FelixJMaxwell/MechanicalKeyboard/Kicad Footprints/arduino_micro_shield.png

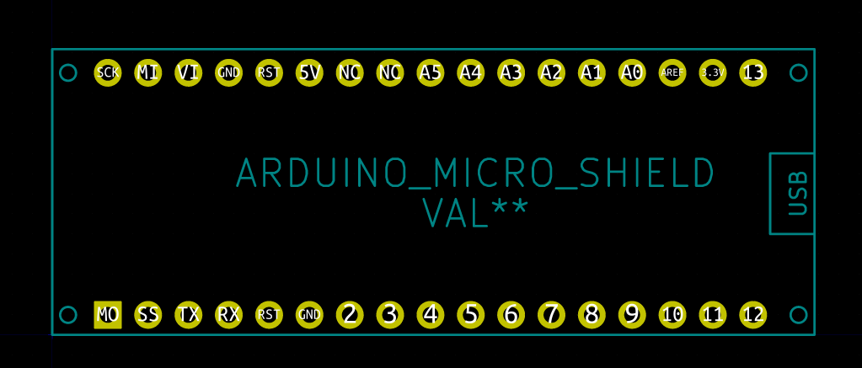
Kicad Footprints/arduino_micro_shield.png
