FelixJMaxwell/MechanicalKeyboard/Kicad Footprints/Stabilizer_Cherry_MX_7u.step

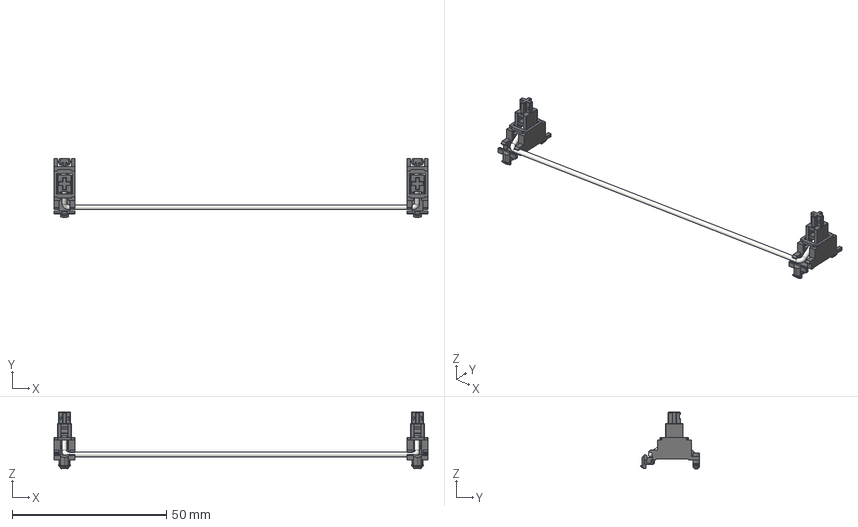
[picture p28: CAD file, 2021-05-09]
Kicad Footprints/Stabilizer_Cherry_MX_7u.step
121.1 x 19.2 x 18.3 mm
