FelixJMaxwell/MechanicalKeyboard/Kicad Footprints/Stabilizer_Cherry_MX_2u.step

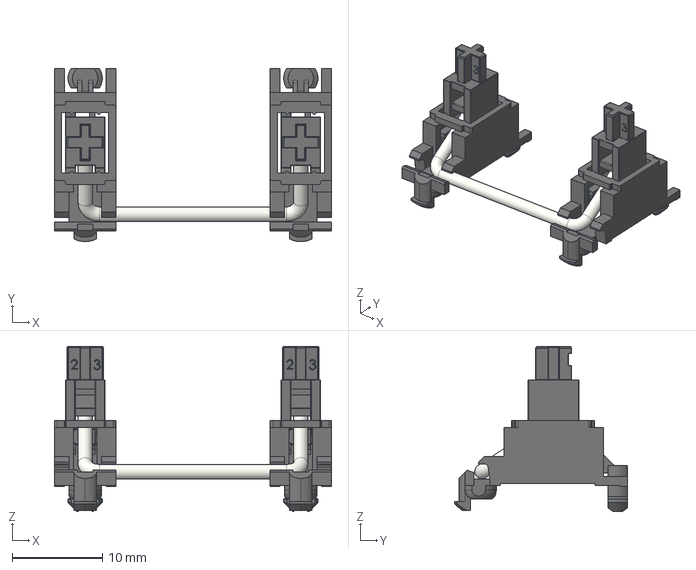
[picture p29: CAD file, 2021-05-09]
Kicad Footprints/Stabilizer_Cherry_MX_2u.step
30.7 x 19.2 x 18.3 mm
