FelixJMaxwell/MechanicalKeyboard/Kicad Footprints/Stabilizer_Cherry_MX_3u.step

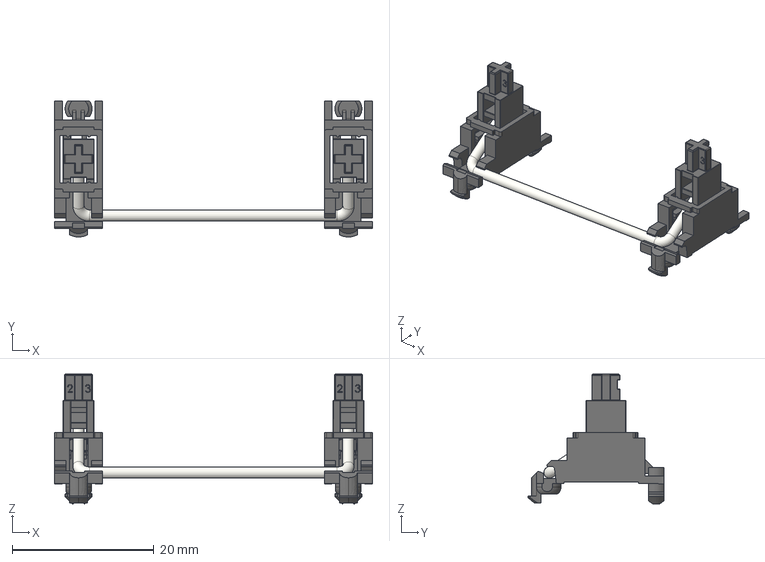
[picture p30: CAD file, 2021-05-09]
Kicad Footprints/Stabilizer_Cherry_MX_3u.step
44.9 x 19.2 x 18.3 mm
