FelixJMaxwell/MechanicalKeyboard/Kicad Footprints/SW_Cherry_MX_PCB.step

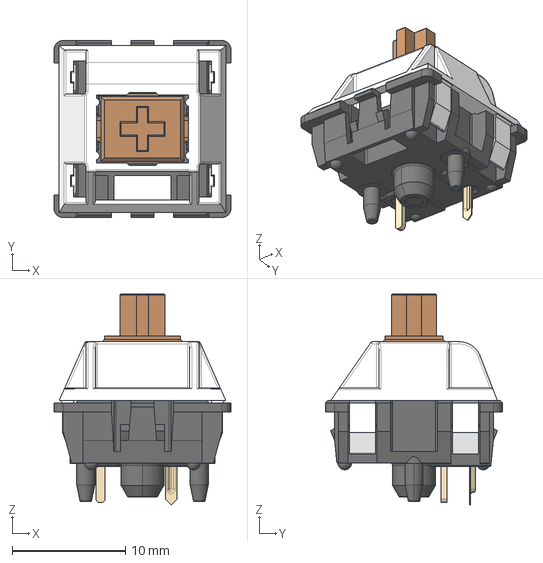
[picture p31: CAD file, 2021-05-09]
Kicad Footprints/SW_Cherry_MX_PCB.step
15.6 x 15.6 x 18.6 mm
