FelixJMaxwell/MechanicalKeyboard/Kicad Footprints/D_SOD-123 Soldered.step

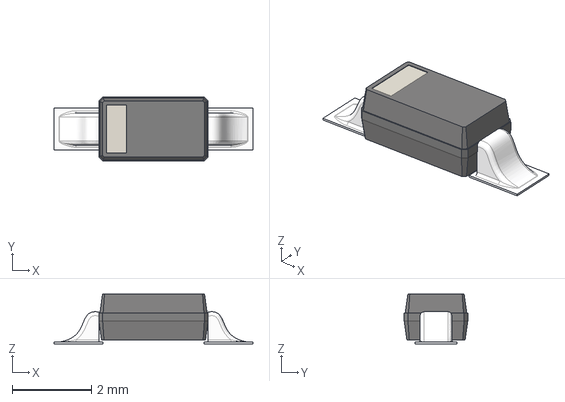
[picture p32: CAD file, 2021-05-04]
Kicad Footprints/D_SOD-123 Soldered.step
5.01 x 1.60 x 1.25 mm
