FelixJMaxwell/MechanicalKeyboard/Kicad Footprints/PJ-3200B.step

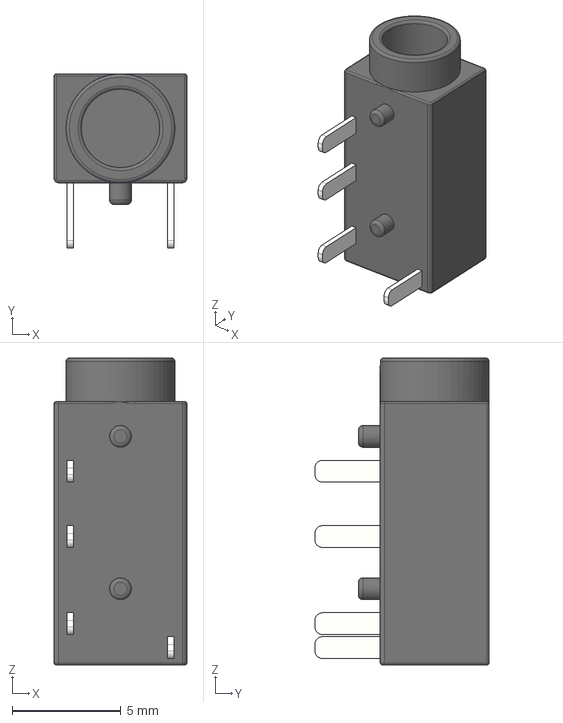
[picture p33: CAD file, 2021-05-04]
Kicad Footprints/PJ-3200B.step
6.10 x 8.00 x 14.1 mm
