FelixJMaxwell/MechanicalKeyboard/Kicad Footprints/tact switch Soldered.step

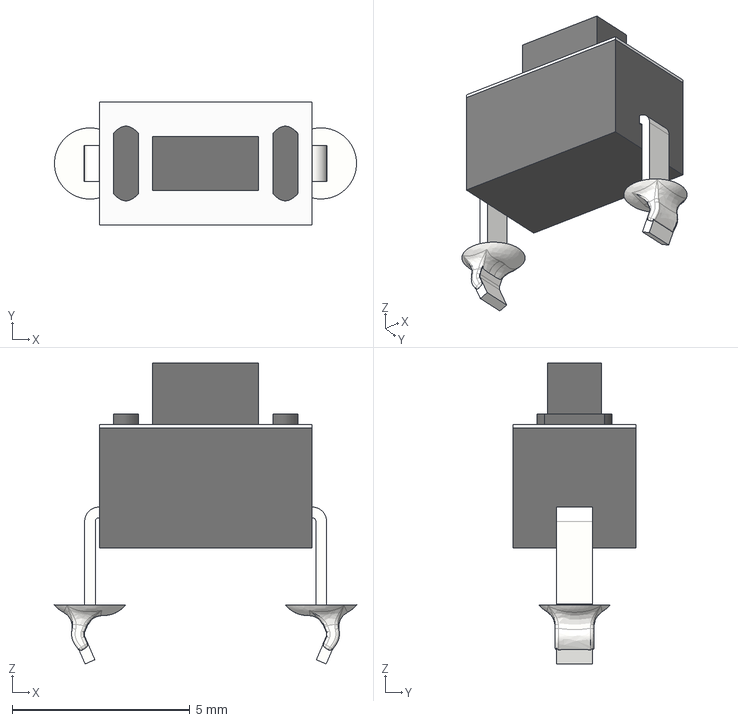
[picture p34: CAD file, 2021-05-04]
Kicad Footprints/tact switch Soldered.step
8.49 x 3.46 x 8.46 mm
