FelixJMaxwell/MechanicalKeyboard/Kicad Footprints/Molex-0548190519.step

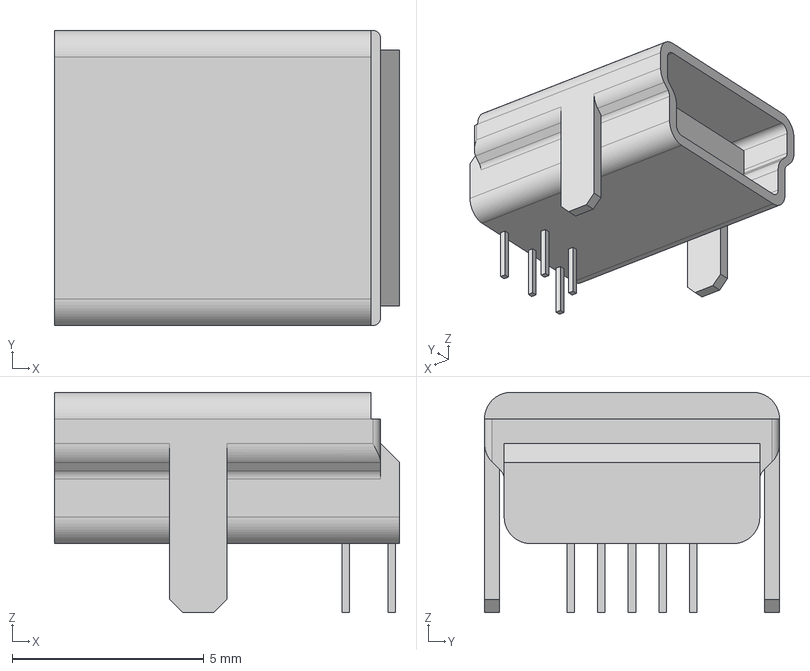
[picture p35: CAD file, 2021-05-04]
Kicad Footprints/Molex-0548190519.step
9.00 x 7.70 x 5.75 mm
