FelixJMaxwell/MechanicalKeyboard/Kicad Footprints/corne-plate acrylic oled left.step

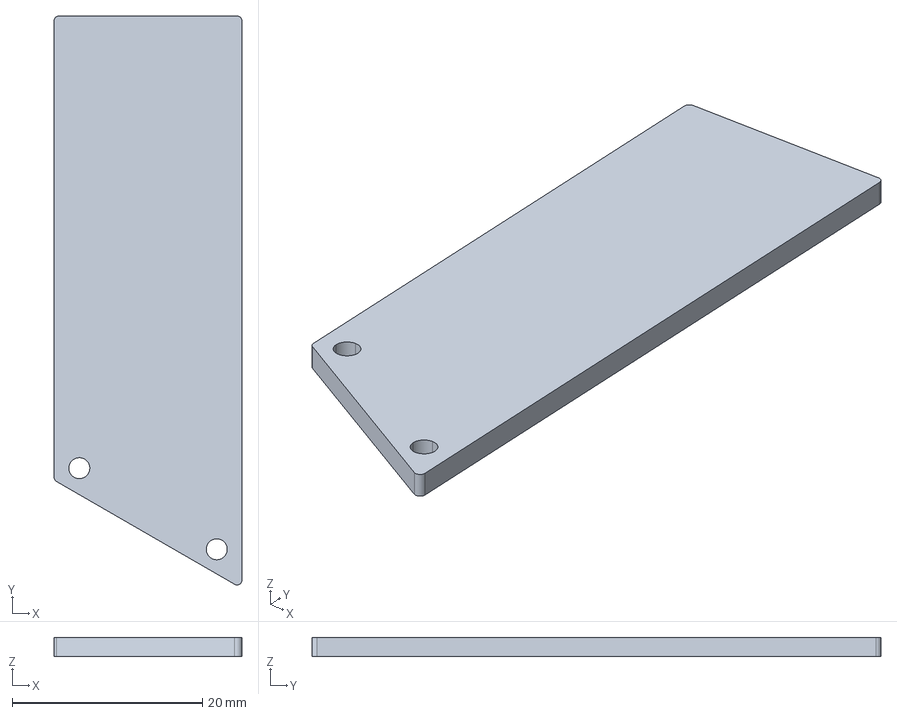
[picture p36: CAD file, 2021-05-04]
Kicad Footprints/corne-plate acrylic oled left.step
19.7 x 59.8 x 2.00 mm
