FelixJMaxwell/MechanicalKeyboard/Kicad Footprints/WS2812B.step

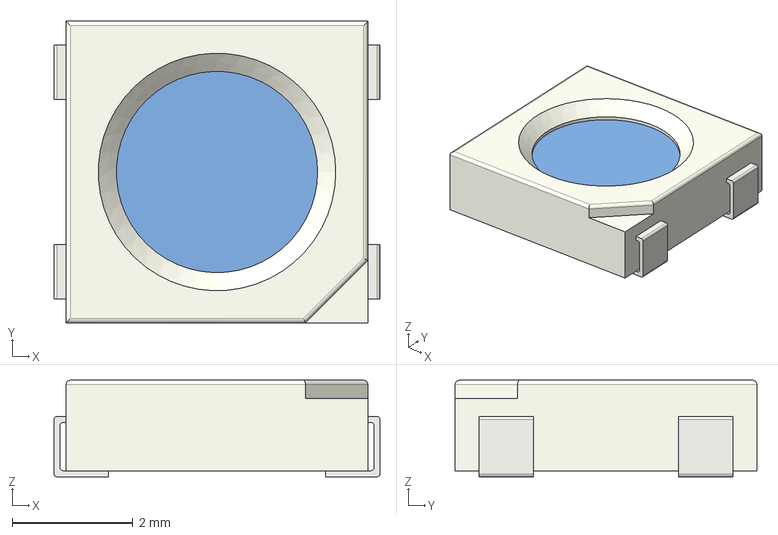
[picture p37: CAD file, 2021-05-04]
Kicad Footprints/WS2812B.step
5.40 x 5.00 x 1.60 mm
