FelixJMaxwell/MechanicalKeyboard/Kicad Footprints/OLED Module with Pins Soldered.step

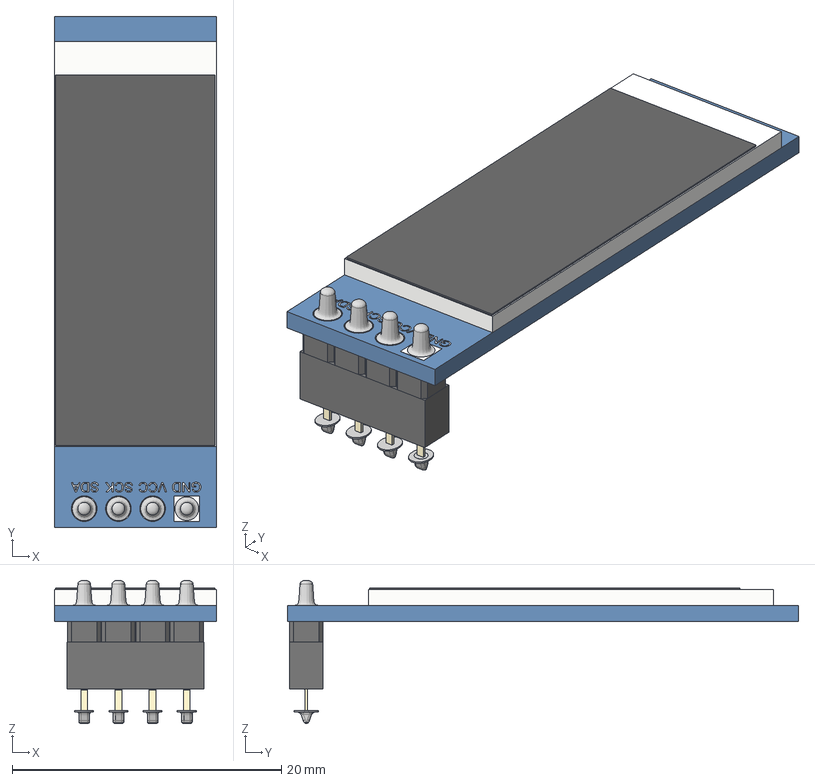
[picture p38: CAD file, 2021-05-04]
Kicad Footprints/OLED Module with Pins Soldered.step
12.1 x 37.9 x 10.6 mm
Pin Socket 1x4
Pin Header 1.4
OLED Module
