FelixJMaxwell/MechanicalKeyboard/Kicad Footprints/pin-header-1x4.step

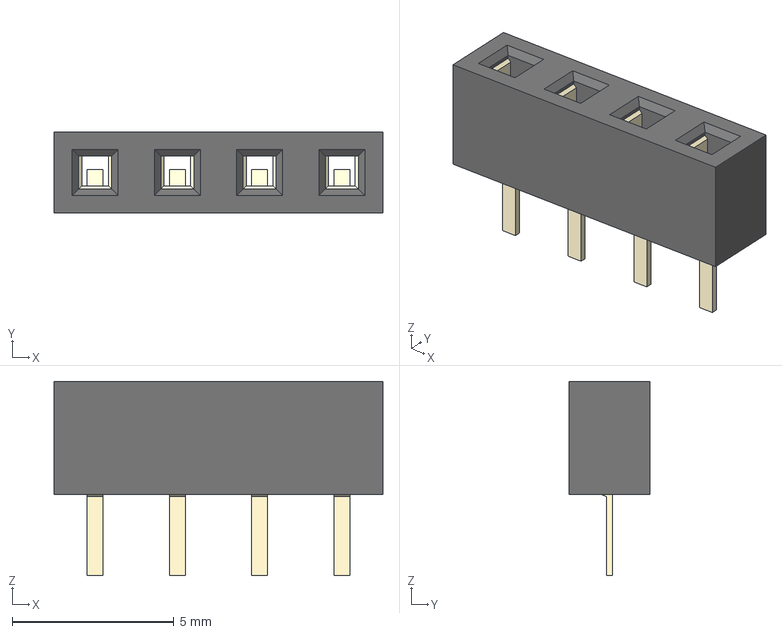
[picture p39: CAD file, 2021-05-04]
Kicad Footprints/pin-header-1x4.step
10.2 x 2.50 x 6.00 mm
