FelixJMaxwell/MechanicalKeyboard/Kicad Footprints/WS2812B Soldered Soldered.step

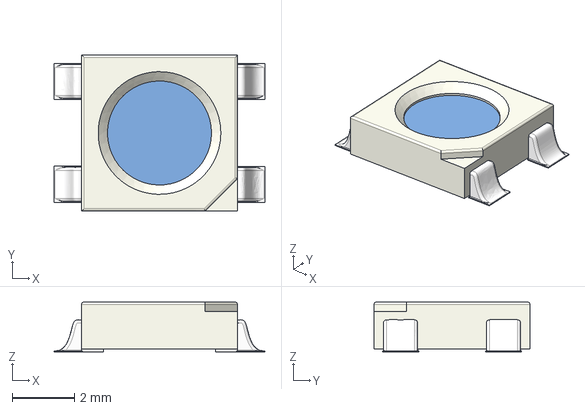
[picture p40: CAD file, 2021-05-04]
Kicad Footprints/WS2812B Soldered Soldered.step
6.76 x 5.00 x 1.60 mm
