FelixJMaxwell/MechanicalKeyboard/Kicad Footprints/YS-SK6812MINI-E Soldered.step

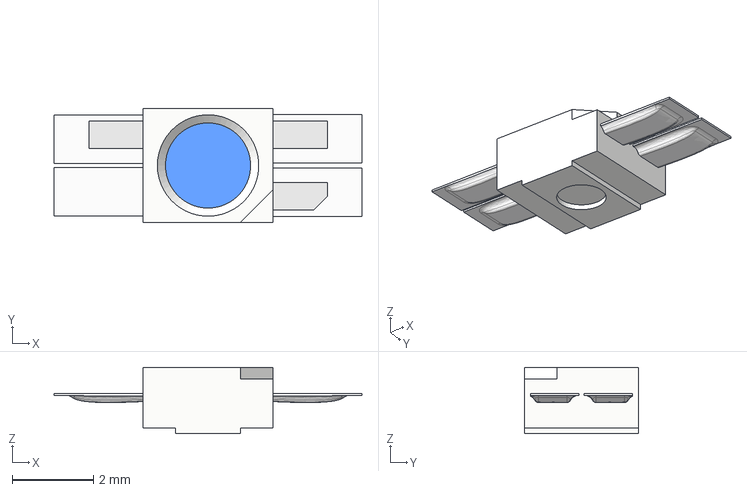
[picture p41: CAD file, 2021-05-04]
Kicad Footprints/YS-SK6812MINI-E Soldered.step
7.59 x 2.80 x 1.63 mm
