FelixJMaxwell/MechanicalKeyboard/Kicad Footprints/corne-plate fr4 top left.step

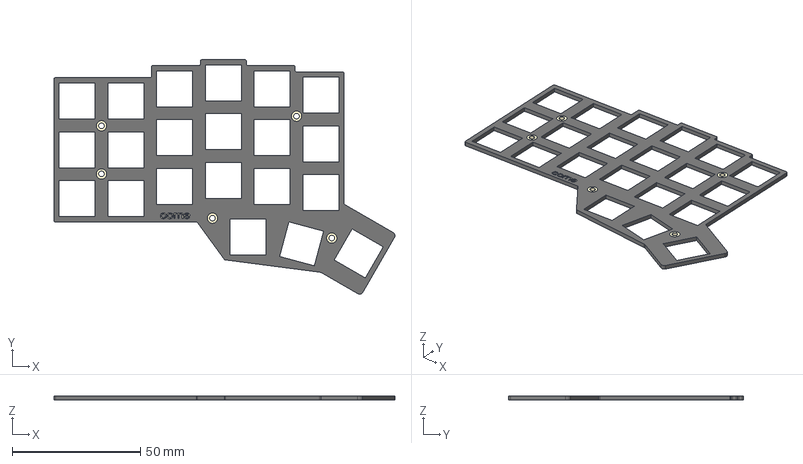
[picture p42: CAD file, 2021-05-04]
Kicad Footprints/corne-plate fr4 top left.step
132.9 x 91.4 x 1.64 mm
