FelixJMaxwell/MechanicalKeyboard/Kicad Footprints/PJ320A Soldered.step

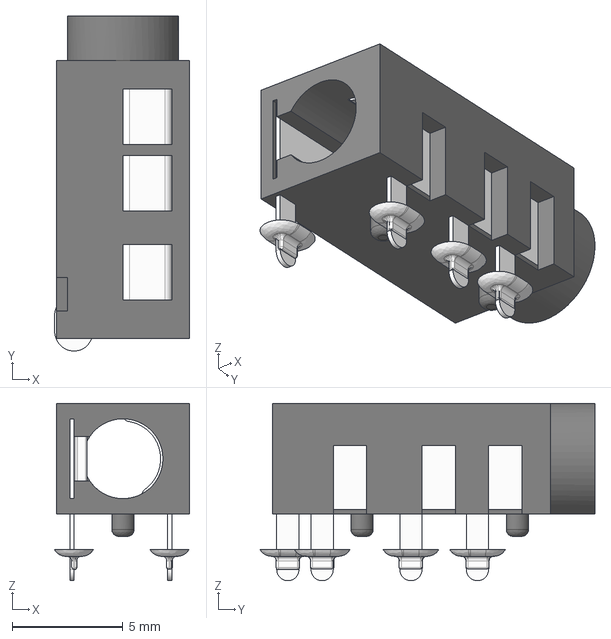
[picture p43: CAD file, 2021-05-04]
Kicad Footprints/PJ320A Soldered.step
6.09 x 15.1 x 8.00 mm
