FelixJMaxwell/MechanicalKeyboard/Kicad Footprints/kailh_choc.step

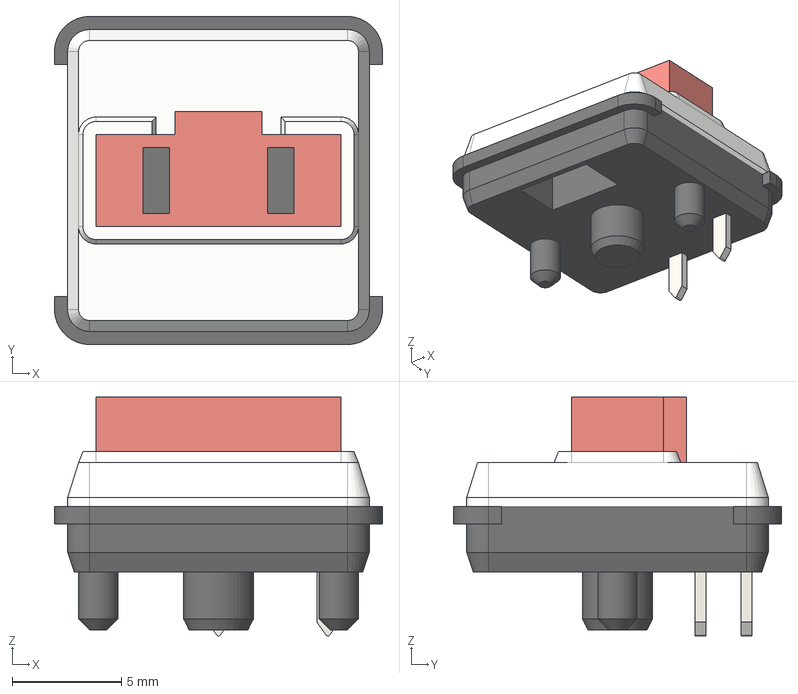
[picture p44: CAD file, 2021-05-04]
Kicad Footprints/kailh_choc.step
15.0 x 15.0 x 10.9 mm
