FelixJMaxwell/MechanicalKeyboard/Kicad Footprints/CherryMX Switch.step

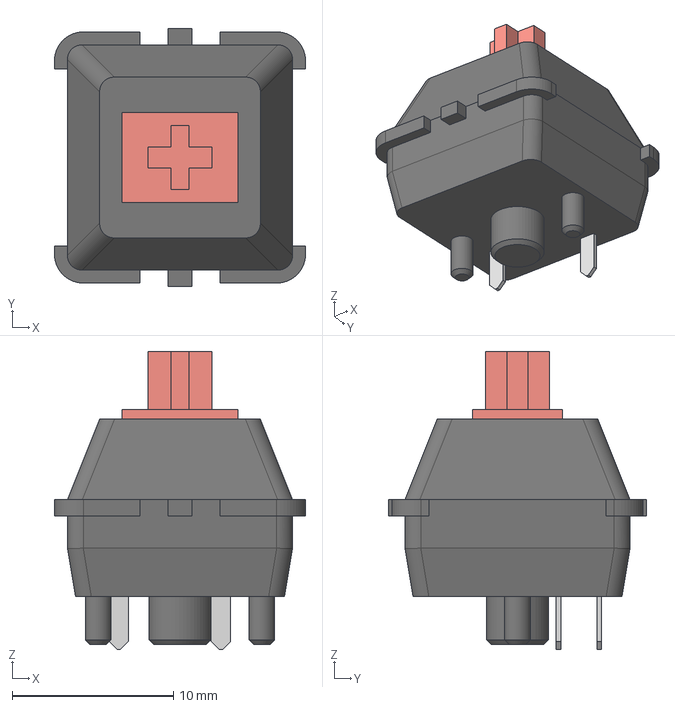
[picture p45: CAD file, 2021-05-04]
Kicad Footprints/CherryMX Switch.step
15.6 x 16.0 x 18.5 mm
