FelixJMaxwell/MechanicalKeyboard/Kicad Footprints/1N4148.step

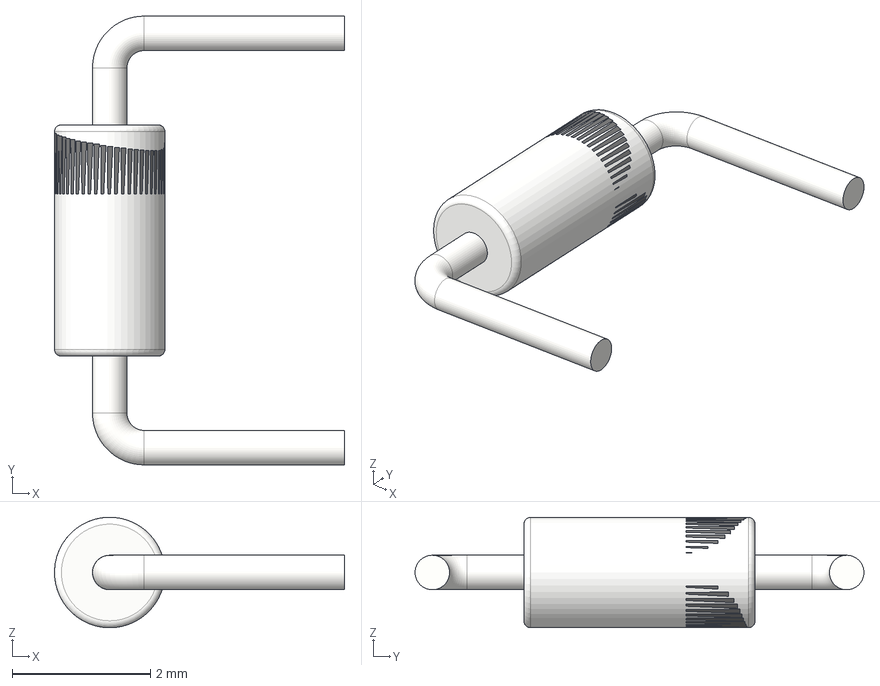
[picture p46: CAD file, 2021-05-04]
Kicad Footprints/1N4148.step
4.20 x 6.50 x 1.60 mm
