FelixJMaxwell/MechanicalKeyboard/Kicad Footprints/corne-plate-rubber-bottom-no-holes.step

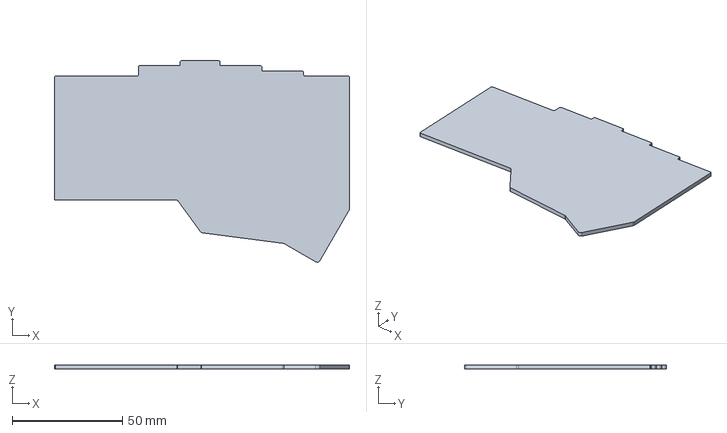
[picture p47: CAD file, 2021-05-04]
Kicad Footprints/corne-plate-rubber-bottom-no-holes.step
133.8 x 91.4 x 2.00 mm
