FelixJMaxwell/MechanicalKeyboard/Kicad Footprints/JST-SR-3.step

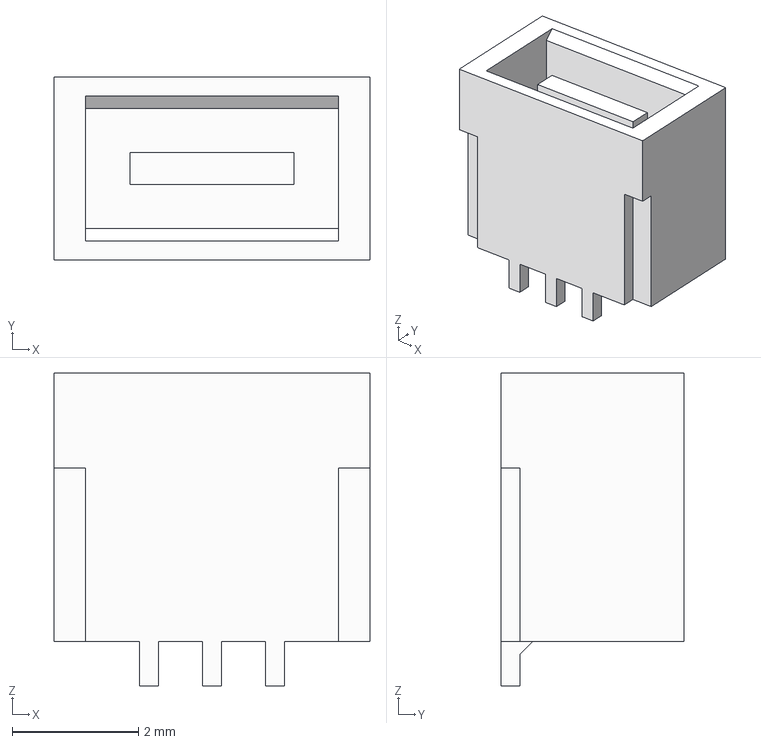
[picture p48: CAD file, 2021-05-04]
Kicad Footprints/JST-SR-3.step
5.00 x 2.90 x 4.95 mm
