FelixJMaxwell/MechanicalKeyboard/Kicad Footprints/corne-plate-acrylic-top-left-no-holes.step

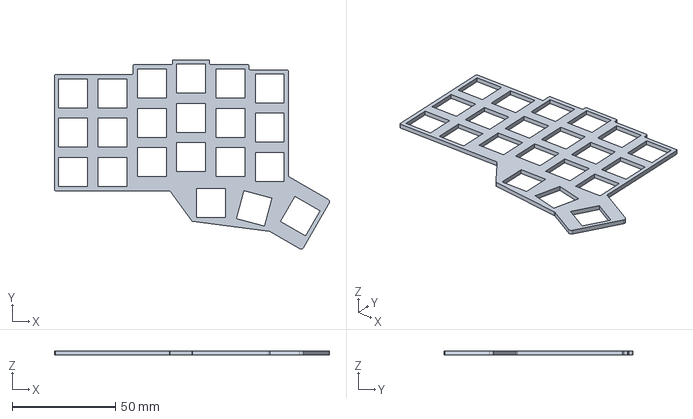
[picture p49: CAD file, 2021-05-04]
Kicad Footprints/corne-plate-acrylic-top-left-no-holes.step
132.9 x 91.4 x 2.00 mm
