FelixJMaxwell/MechanicalKeyboard/Kicad Footprints/D_SOD-123.step

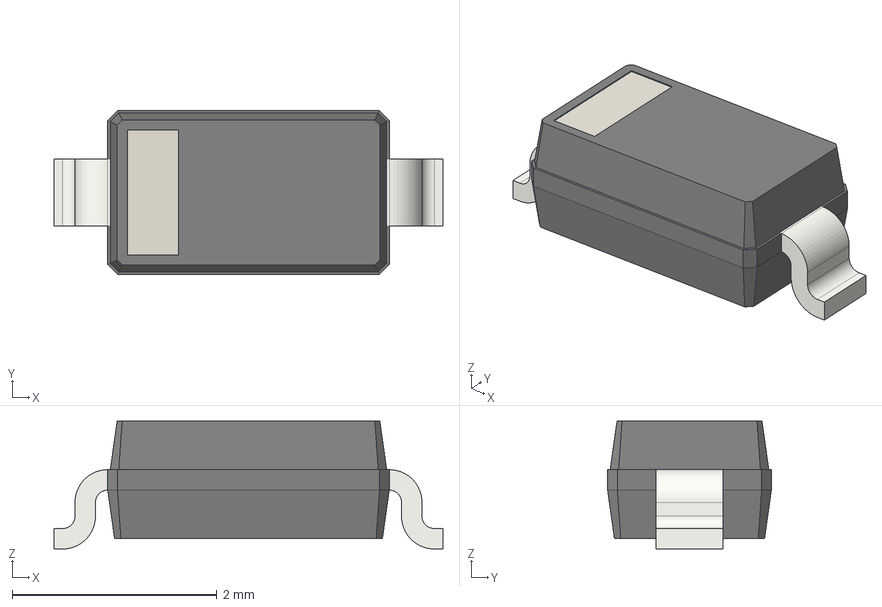
[picture p50: CAD file, 2021-05-04]
Kicad Footprints/D_SOD-123.step
3.80 x 1.60 x 1.25 mm
