FelixJMaxwell/MechanicalKeyboard/Kicad Footprints/YS-SK6812MINI-E.step

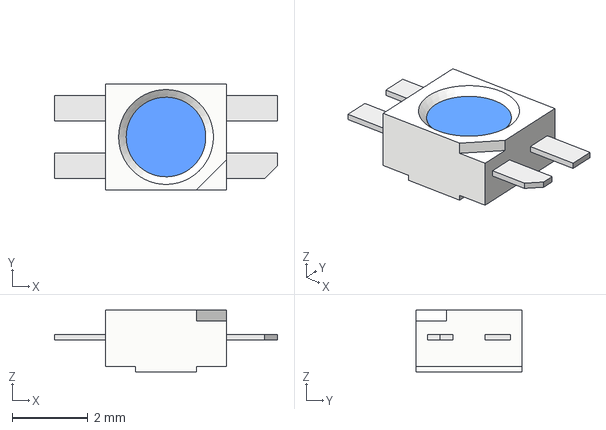
[picture p51: CAD file, 2021-05-04]
Kicad Footprints/YS-SK6812MINI-E.step
5.88 x 2.80 x 1.63 mm
