FelixJMaxwell/MechanicalKeyboard/Kicad Footprints/tact-switch.step

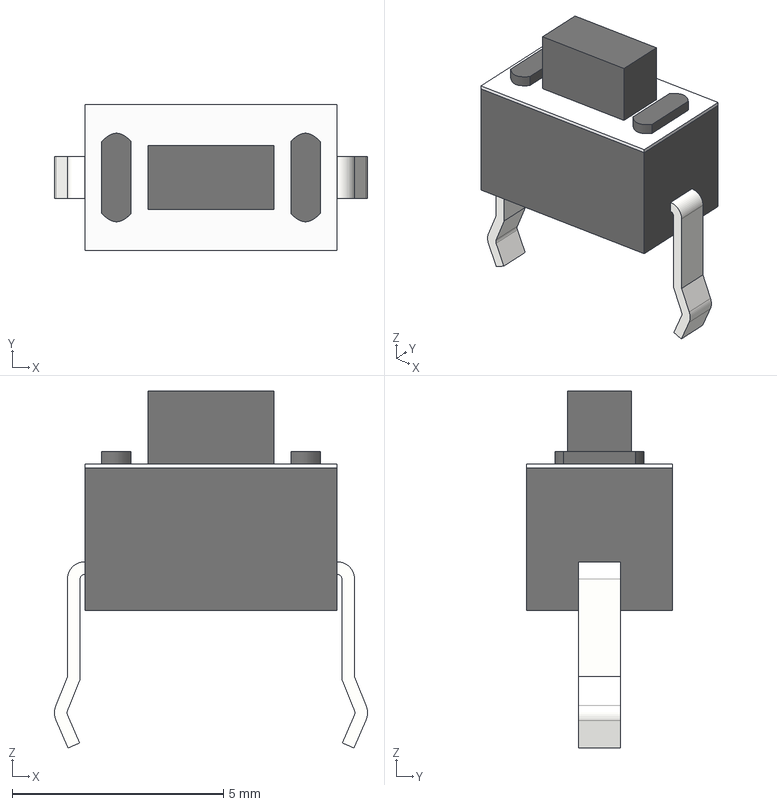
[picture p52: CAD file, 2021-05-04]
Kicad Footprints/tact-switch.step
7.42 x 3.46 x 8.46 mm
