FelixJMaxwell/MechanicalKeyboard/Kicad Footprints/JST-SR-4.step

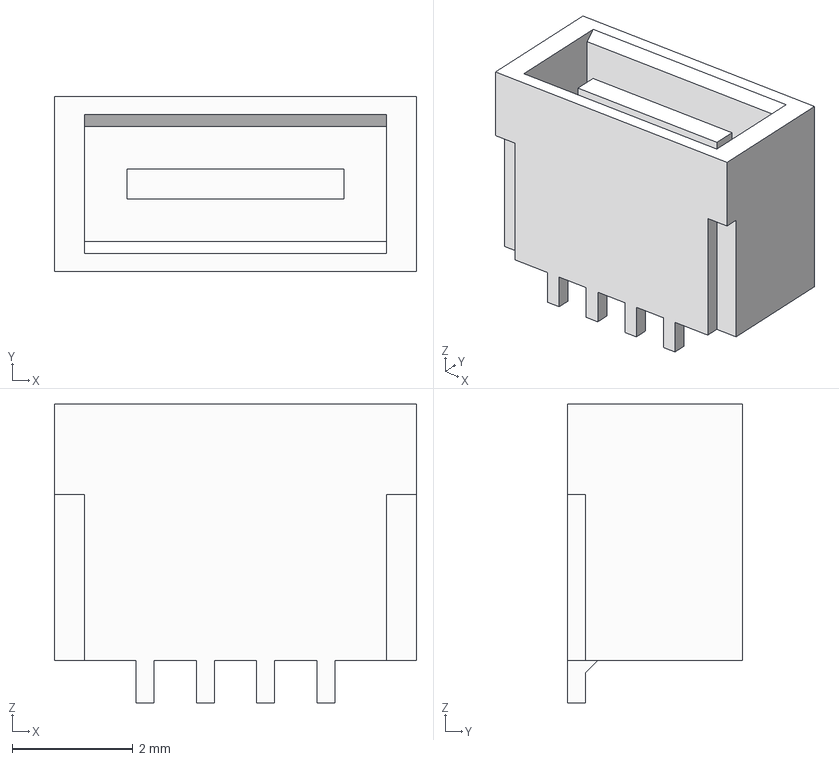
[picture p53: CAD file, 2021-05-04]
Kicad Footprints/JST-SR-4.step
6.00 x 2.90 x 4.95 mm
