FelixJMaxwell/MechanicalKeyboard/Kicad Footprints/SSD1306_OLED-0.91-128x32.step

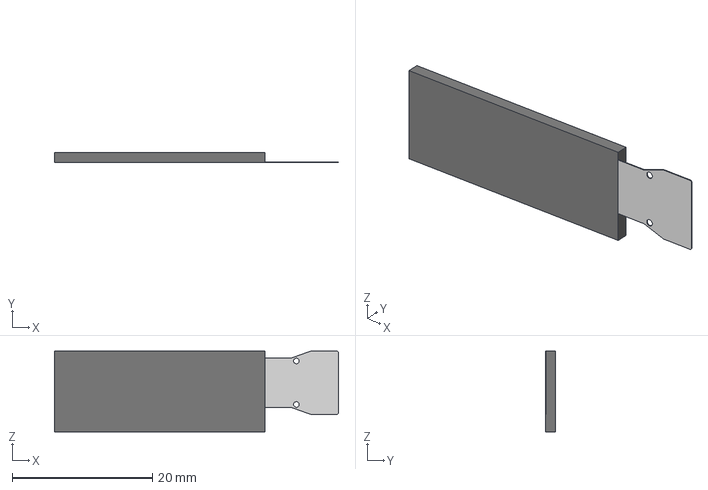
[picture p54: CAD file, 2021-05-04]
Kicad Footprints/SSD1306_OLED-0.91-128x32.step
40.5 x 1.45 x 11.5 mm
