FelixJMaxwell/MechanicalKeyboard/Kicad Footprints/ProMicro.step

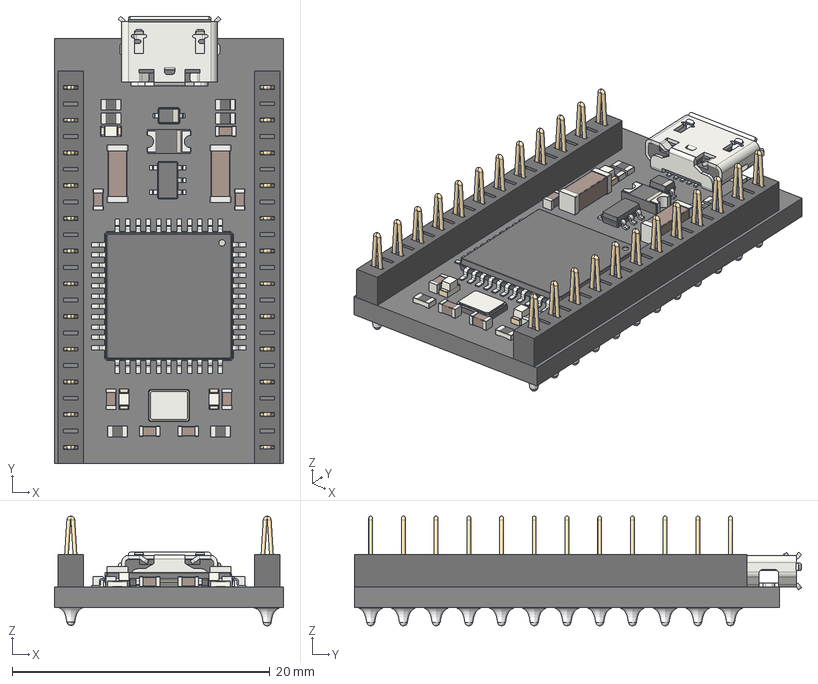
[picture p55: CAD file, 2021-05-04]
Kicad Footprints/ProMicro.step
17.8 x 34.7 x 8.54 mm
TQFP-44_10x10mm_P0.8mm
USB_Micro-B_Molex_47346-0001
R_0603 x 6
LED_0603_1608Metric x 3
C_0603_1608Metric x 8
Crystal_SMD_3225-4Pin_3.2x2.5mm
D_SOD-323
D_1206_3216Metric
TSOT-23-5
C_1806_4516Metric x 2
conthrough x 2
