FelixJMaxwell/MechanicalKeyboard/Kicad Footprints/HRO  TYPE-C-31-M-12.step

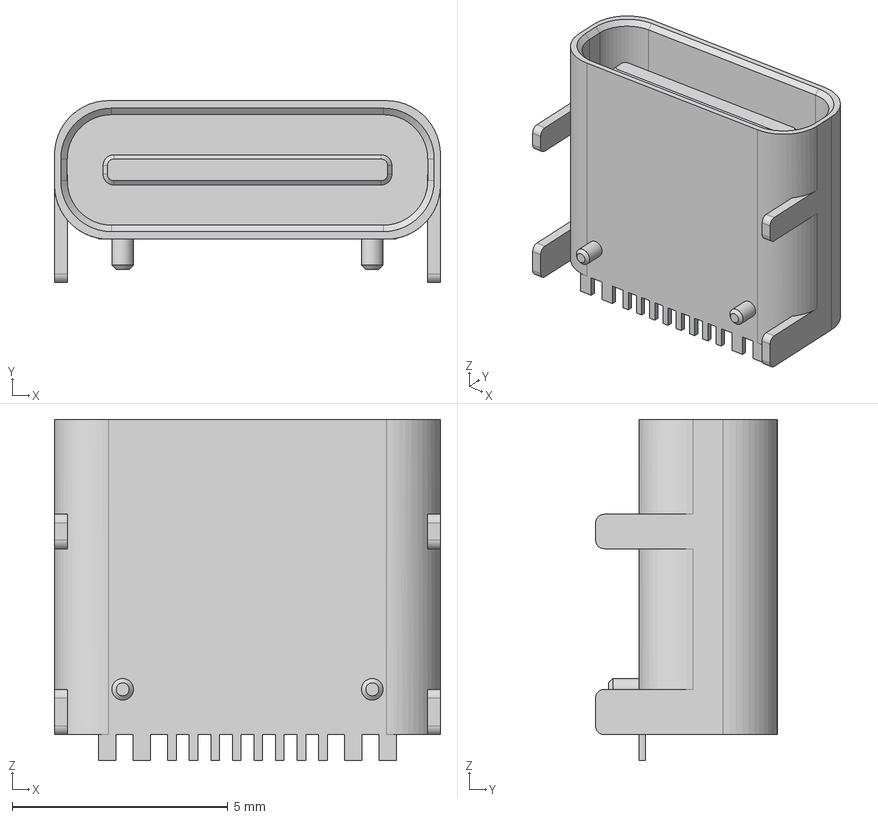
[picture p56: CAD file, 2021-05-04]
Kicad Footprints/HRO TYPE-C-31-M-12.step
8.94 x 4.21 x 7.90 mm
