FelixJMaxwell/MechanicalKeyboard/Kicad Footprints/MX Series-Cherry Key.step

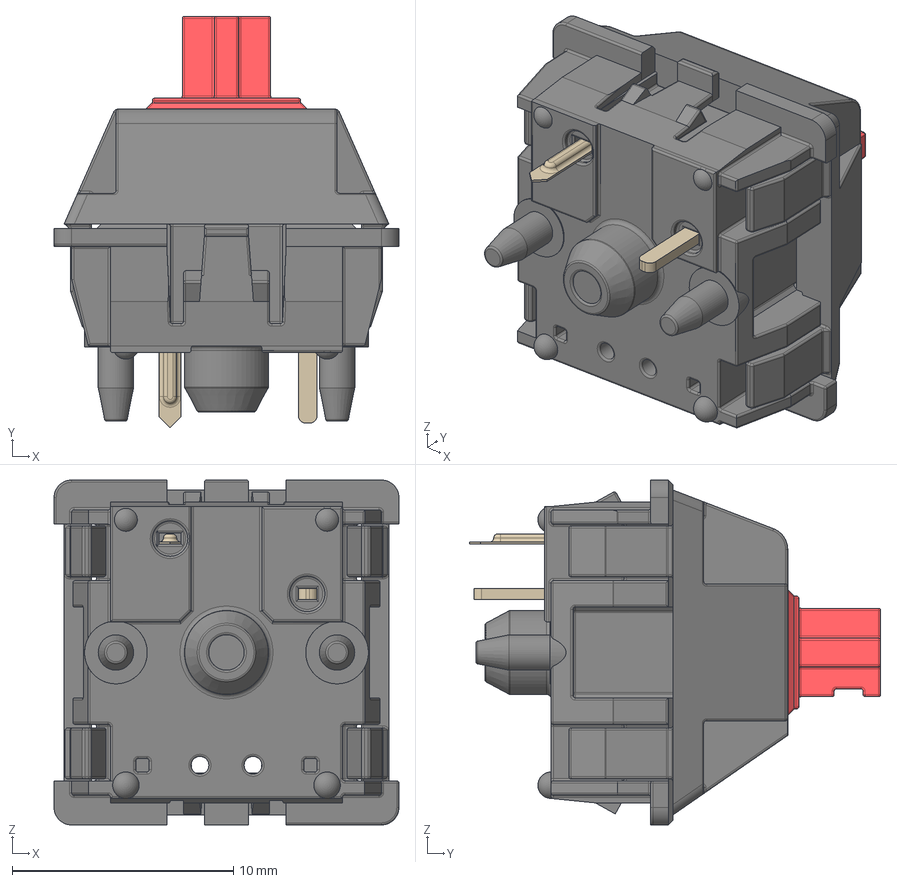
[picture p57: CAD file, 2021-05-04]
Kicad Footprints/MX Series-Cherry Key.step
15.6 x 18.6 x 15.6 mm
