FelixJMaxwell/MechanicalKeyboard/Kicad Footprints/kailh cherry socket soldered.step

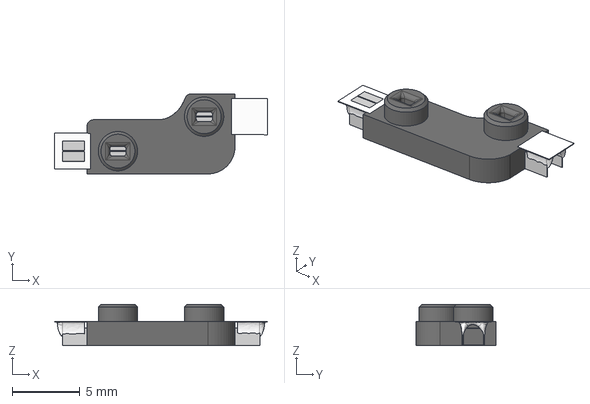
[picture p58: CAD file, 2021-05-04]
Kicad Footprints/kailh cherry socket soldered.step
15.7 x 5.89 x 3.05 mm
