FelixJMaxwell/MechanicalKeyboard/Kicad Footprints/Kailh-CherryMX-Socket.step

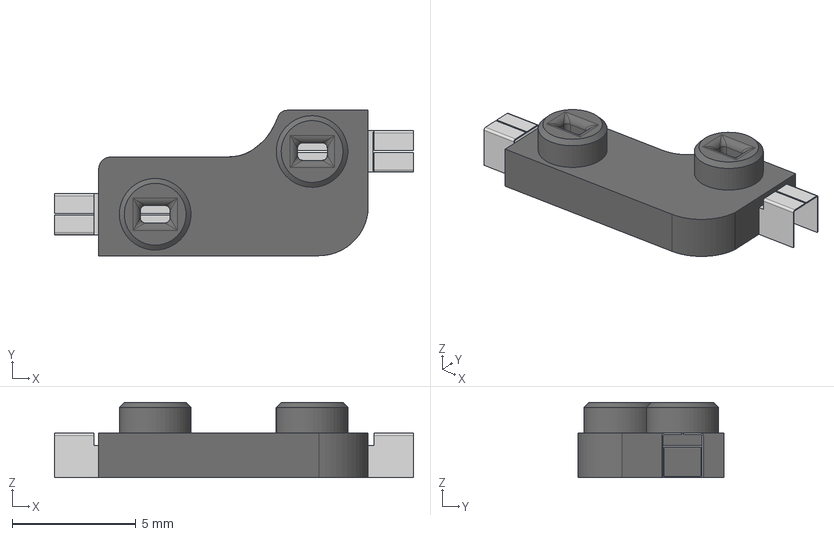
[picture p59: CAD file, 2021-05-04]
Kicad Footprints/Kailh-CherryMX-Socket.step
14.5 x 5.89 x 3.05 mm
