FelixJMaxwell/MechanicalKeyboard/SplitKeyboard/SplitKeyboard.kicad_pcb

## KiCad design SplitKeyboard/SplitKeyboard.kicad_pcb (2021-08-08)

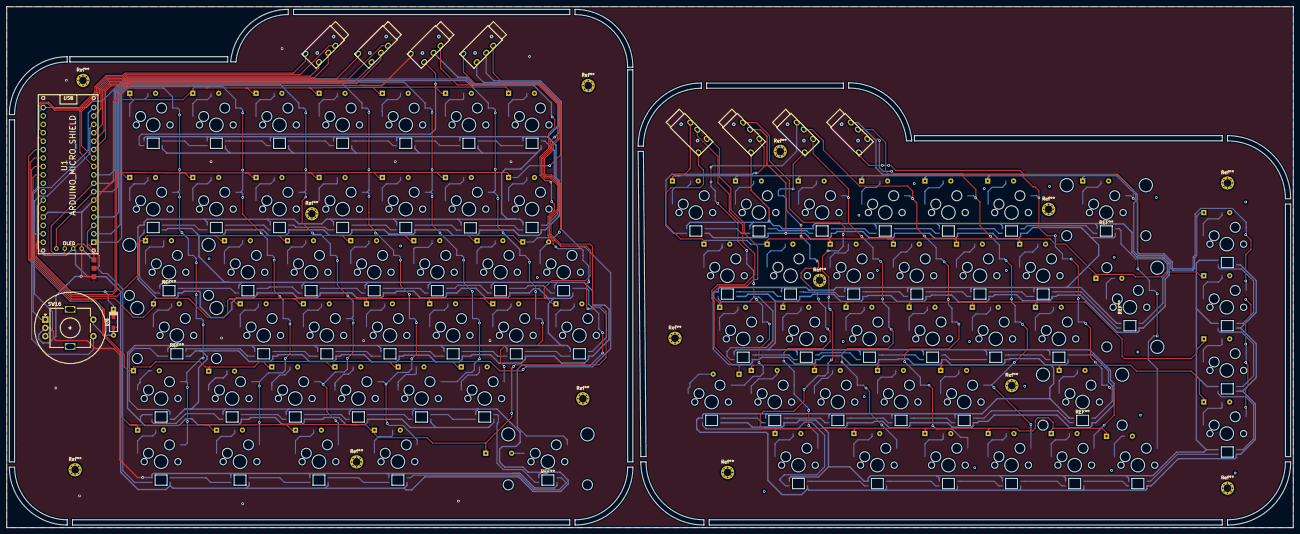
[picture p68: board SplitKeyboard.kicad_pcb from above]

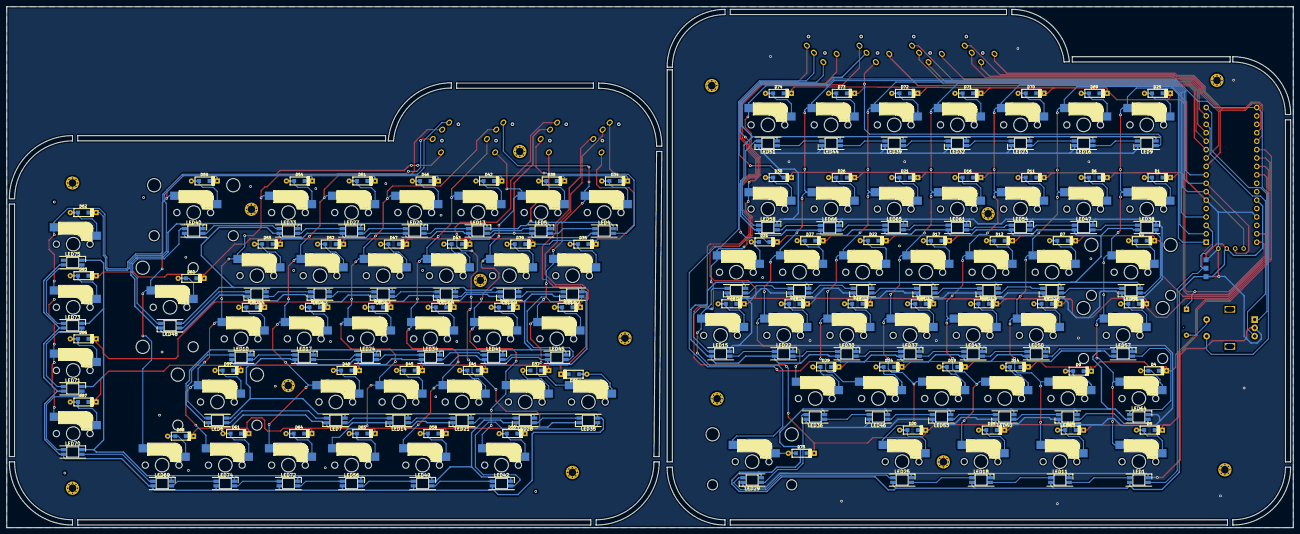
[picture p69: board SplitKeyboard.kicad_pcb from below]

Board: 2 copper layers, 388.1 x 157.2 mm, 252 parts (150 on the bottom side), 105 nets.

Parts:
D1, D2, D3, D4, D5, D6, D7, D8, D9, D10, D11, D12, D13, D14, D15, D16, D17, D18, D19, D20, D21, D22, D23, D24, D25, D26, D27, D28, D29, D30, D31, D32, D33, D34, D35, D36, D37, D38, D39, D40, D41, D42, D43, D44, D45, D46, D47, D48, D49, D50, D51, D52, D53, D54, D55, D56, D57, D58, D59, D60, D61, D62, D63, D64, D65, D66, D67, D68, D69, D70, D71, D72, D73, D74, D75, D76: 1N4148; D_SOD123_axial
J1: LED; StripLED_rev
JTRRS1, JTRRS2, JTRRS3, JTRRS4, JTRRS5, JTRRS6, JTRRS7, JTRRS8: 4PIN; TRRS-PJ-320A
LED1, LED2, LED3, LED4, LED5, LED6, LED7, LED8, LED9, LED10, LED11, LED12, LED13, LED14, LED15, LED16, LED17, LED18, LED19, LED20, LED21, LED22, LED23, LED24, LED25, LED26, LED27, LED28, LED29, LED30, LED31, LED32, LED33, LED34, LED35, LED36, LED37, LED38, LED39, LED40, LED41, LED42, LED43, LED44, LED45, LED46, LED47, LED48, LED49, LED50, LED51, LED52, LED53, LED54, LED55, LED56, LED57, LED58, LED59, LED60, LED61, LED62, LED63, LED64, LED65, LED66, LED67, LED68, LED69, LED70, LED71, LED72, LED73, LED74, LED75: YS-SK6812MINI-E; YS-SK6812MINI-E_2
P2: OLED; OLED_v2
Ref**: Val**; M2_HOLE_v3
Ref**#2, Ref**#3, Ref**#4, Ref**#5, Ref**#6, Ref**#7, Ref**#8, Ref**#9, Ref**#10, Ref**#11, Ref**#12, Ref**#13, Ref**#14: Val**; M2_HOLE_v3
SW0, SW1, SW2, SW3, SW4, SW5, SW6, SW7, SW8, SW9, SW14, SW15: SW_Push; CherryMX_Hotswap
SW10: SW_DownArrow; CherryMX_Hotswap
SW13: SW_RightArrow; CherryMX_Hotswap
SW16: Rotary_Encoder_Switch; RotaryEncoder_Alps_EC11E-Switch_Vertical_H20mm
SW+1: SW_Push; CherryMX_Hotswap
SWBarrita1: SW_Push; CherryMX_Hotswap
SWCtrlright1: SW_Push; CherryMX_Hotswap
SWF2, SWF4, SWF5, SWF6, SWF8, SWF12: SW_Push; CherryMX_Hotswap
SWLeftArrow1: SW_Push; CherryMX_Hotswap
SWUpArrow1: SW_Push; CherryMX_Hotswap
SWa1: SW_Push; CherryMX_Hotswap
SWaltgr1: SW_Push; CherryMX_Hotswap
SWaltleft1: SW_Push; CherryMX_Hotswap
SWb1: SW_Push; CherryMX_Hotswap
SWbackslash1: SW_Push; CherryMX_Hotswap
SWbloqmayus1: SW_Push; CherryMX_Hotswap
SWc1: SW_Push; CherryMX_Hotswap
SWcomilla1: SW_Push; CherryMX_Hotswap
SWcomma1: SW_Push; CherryMX_Hotswap
SWctrl1: SW_Push; CherryMX_Hotswap
SWd1: SW_Push; CherryMX_Hotswap
SWe1: SW_Push; CherryMX_Hotswap
SWend1: SW_Push; CherryMX_Hotswap
SWenter1: SW_Push; CherryMX_Hotswap
SWesc1: SW_Push; CherryMX_Hotswap
SWf1: SW_Push; CherryMX_Hotswap
SWfn1: SW_Push; CherryMX_Hotswap
SWg1: SW_Push; CherryMX_Hotswap
SWguion1: SW_Push; CherryMX_Hotswap
SWh1: SW_Push; CherryMX_Hotswap
SWhome1: SW_Push; CherryMX_Hotswap
SWi1: SW_Push; CherryMX_Hotswap
SWj1: SW_Push; CherryMX_Hotswap
SWk1: SW_Push; CherryMX_Hotswap
SWl1: SW_Push; CherryMX_Hotswap
SWm1: SW_Push; CherryMX_Hotswap
SWn1: SW_Push; CherryMX_Hotswap
SWo1: SW_Push; CherryMX_Hotswap
SWp1: SW_Push; CherryMX_Hotswap
SWpgdown1: SW_Push; CherryMX_Hotswap
SWpgup1: SW_Push; CherryMX_Hotswap
SWpunto1: SW_Push; CherryMX_Hotswap
SWq1: SW_Push; CherryMX_Hotswap
SWr1: SW_Push; CherryMX_Hotswap
SWs1: SW_Push; CherryMX_Hotswap
SWshift1: SW_Push; CherryMX_Hotswap
SWshiftright1: SW_Push; CherryMX_Hotswap
SWsigno1: SW_Push; CherryMX_Hotswap
SWspace1: SW_Push; CherryMX_Hotswap
SWt1: SW_Push; CherryMX_Hotswap
SWtab1: SW_Push; CherryMX_Hotswap
SWu1: SW_Push; CherryMX_Hotswap
SWv1: SW_Push; CherryMX_Hotswap
SWw1: SW_Push; CherryMX_Hotswap
SWwin1: SW_Push; CherryMX_Hotswap
SWx1: SW_Push; CherryMX_Hotswap
SWy1: SW_Push; CherryMX_Hotswap
SWz1: SW_Push; CherryMX_Hotswap
SW{1: SW_Push; CherryMX_Hotswap
SW}1: SW_Push; CherryMX_Hotswap
U1: ARDUINO_MICRO_SHIELD

Connections:
Columna2: JTRRS4.1, U1.A1
Columna3: JTRRS4.2, U1.5
Columna4: JTRRS4.3, U1.6
Columna5: JTRRS3.3, U1.7
Columna6: JTRRS3.2, U1.8
Columna7: JTRRS3.1, U1.11
Columna8: JTRRS3.4, U1.9
Columna9: SW6.2, SW16.S1, SWF12.2, SWh1.2, SWspace1.2, SWy1.2, U1.13
Columna10: SW5.2, SWF8.2, SWb1.2, SWg1.2, SWt1.2, U1.4
Columna11: P2.2, SW4.2, SWF6.2, SWf1.2, SWr1.2, SWv1.2, U1.3
Columna12: P2.1, SW3.2, SWF5.2, SWc1.2, SWd1.2, SWe1.2, SWfn1.2, U1.2
Columna13: SW2.2, SWF4.2, SWaltleft1.2, SWs1.2, SWw1.2, SWx1.2, U1.RX
Columna14: SW1.2, SWF2.2, SWa1.2, SWq1.2, SWwin1.2, SWz1.2, U1.SS
Columna15: SWBarrita1.2, SWbloqmayus1.2, SWctrl1.2, SWesc1.2, SWshift1.2, SWtab1.2, U1.MO
Columna16: JTRRS4.4, U1.A0
Fila0: D25.1, D69.1, D70.1, D71.1, D72.1, D73.1, D74.1, D76.1, U1.SCK
Fila1: D1.1, D6.1, D11.1, D16.1, D21.1, D26.1, D30.1, JTRRS5.4, U1.MI
Fila3: D3.1, D8.1, D13.1, D18.1, D23.1, D28.1, D32.1, JTRRS5.2, U1.A4
Fila4: D4.1, D9.1, D14.1, D19.1, D24.1, D29.1, JTRRS5.3, U1.A3
Fila5: D5.1, D10.1, D15.1, D20.1, D75.1, JTRRS6.4, U1.A2
Fila6: D2.1, D7.1, D12.1, D17.1, D22.1, D27.1, D31.1, JTRRS5.1, U1.A5
GND: J1.3, JTRRS6.1, LED1.3, LED2.3, LED3.3, LED8.3, LED9.3, LED11.3, LED12.3, LED15.3, LED16.3, LED18.3, LED19.3, LED22.3, LED23.3, LED25.3, LED26.3, LED29.3, LED30.3, LED31.3, LED32.3, LED36.3, LED37.3, LED38.3, LED39.3, LED43.3, LED44.3, LED46.3, LED47.3, LED50.3, LED51.3, LED53.3, LED54.3, LED57.3, LED58.3, LED60.3, LED61.3, LED63.3, LED64.3, LED65.3, LED66.3, P2.4, SW16.C, U1.GND
LED: J1.2, LED1.4, U1.TX
LEDTRRS: JTRRS6.2, LED9.2
unnamed: D1.2, SWBarrita1.1
unnamed: D2.2, SWtab1.1
unnamed: D3.2, SWbloqmayus1.1
unnamed: D4.2, SWshift1.1
unnamed: D5.2, SWctrl1.1
unnamed: D6.2, SW1.1
unnamed: D7.2, SWq1.1
unnamed: D8.2, SWa1.1
unnamed: D9.2, SWz1.1
unnamed: D10.2, SWwin1.1
unnamed: D11.2, SW2.1
unnamed: D12.2, SWw1.1
unnamed: D13.2, SWs1.1
unnamed: D14.2, SWx1.1
unnamed: D15.2, SWaltleft1.1
unnamed: D16.2, SW3.1
unnamed: D17.2, SWe1.1
unnamed: D18.2, SWd1.1
unnamed: D19.2, SWc1.1
unnamed: D20.2, SWfn1.1
unnamed: D21.2, SW4.1
unnamed: D22.2, SWr1.1
unnamed: D23.2, SWf1.1
unnamed: D24.2, SWv1.1
unnamed: D25.2, SWesc1.1
unnamed: D26.2, SW5.1
unnamed: D27.2, SWt1.1
unnamed: D28.2, SWg1.1
unnamed: D29.2, SWb1.1
unnamed: D30.2, SW6.1
unnamed: D31.2, SWy1.1
unnamed: D32.2, SWh1.1
unnamed: D69.2, SWF2.1
unnamed: D70.2, SWF4.1
unnamed: D71.2, SWF5.1
unnamed: D72.2, SWF6.1
unnamed: D73.2, SWF8.1
unnamed: D74.2, SWF12.1
unnamed: D75.2, SWspace1.1
unnamed: D76.2, SW16.S2
unnamed: LED1.2, LED11.4
unnamed: LED2.2, LED3.4
unnamed: LED2.4, LED8.2
unnamed: LED11.2, LED18.4
unnamed: LED12.2, LED19.4
unnamed: LED3.2, LED12.4
unnamed: LED8.4, LED15.2
unnamed: LED15.4, LED22.2
unnamed: LED9.4, LED16.2
unnamed: LED16.4, LED23.2
unnamed: LED18.2, LED25.4
unnamed: LED19.2, LED26.4
unnamed: LED22.4, LED30.2
unnamed: LED23.4, LED32.2
unnamed: LED25.2, LED29.4
unnamed: LED26.2, LED31.4
unnamed: LED29.2, LED36.4
unnamed: LED30.4, LED37.2
unnamed: LED31.2, LED38.4
unnamed: LED32.4, LED39.2
unnamed: LED36.2, LED46.4
unnamed: LED37.4, LED43.2
unnamed: LED38.2, LED47.4
unnamed: LED39.4, LED44.2
unnamed: LED43.4, LED50.2
unnamed: LED44.4, LED51.2
unnamed: LED46.2, LED53.4
unnamed: LED47.2, LED54.4
unnamed: LED50.4, LED57.2
unnamed: LED51.4, LED58.2
unnamed: LED53.2, LED60.4
unnamed: LED54.2, LED61.4
unnamed: LED57.4, LED64.2
unnamed: LED58.4, LED66.2
unnamed: LED60.2, LED63.4
unnamed: LED61.2, LED65.4
unnamed: LED63.2, LED64.4
unnamed: LED65.2, LED66.4
VCC: J1.1, JTRRS6.3, LED1.1, LED2.1, LED3.1, LED8.1, LED9.1, LED11.1, LED12.1, LED15.1, LED16.1, LED18.1, LED19.1, LED22.1, LED23.1, LED25.1, LED26.1, LED29.1, LED30.1, LED31.1, LED32.1, LED36.1, LED37.1, LED38.1, LED39.1, LED43.1, LED44.1, LED46.1, LED47.1, LED50.1, LED51.1, LED53.1, LED54.1, LED57.1, LED58.1, LED60.1, LED61.1, LED63.1, LED64.1, LED65.1, LED66.1, P2.3, U1.5V
en1: SW16.B, U1.10
en2: SW16.A, U1.12
