FelixJMaxwell/MechanicalKeyboard/MacroPad/MacroPad.kicad_pcb

## KiCad design MacroPad/MacroPad.kicad_pcb (2021-05-10)

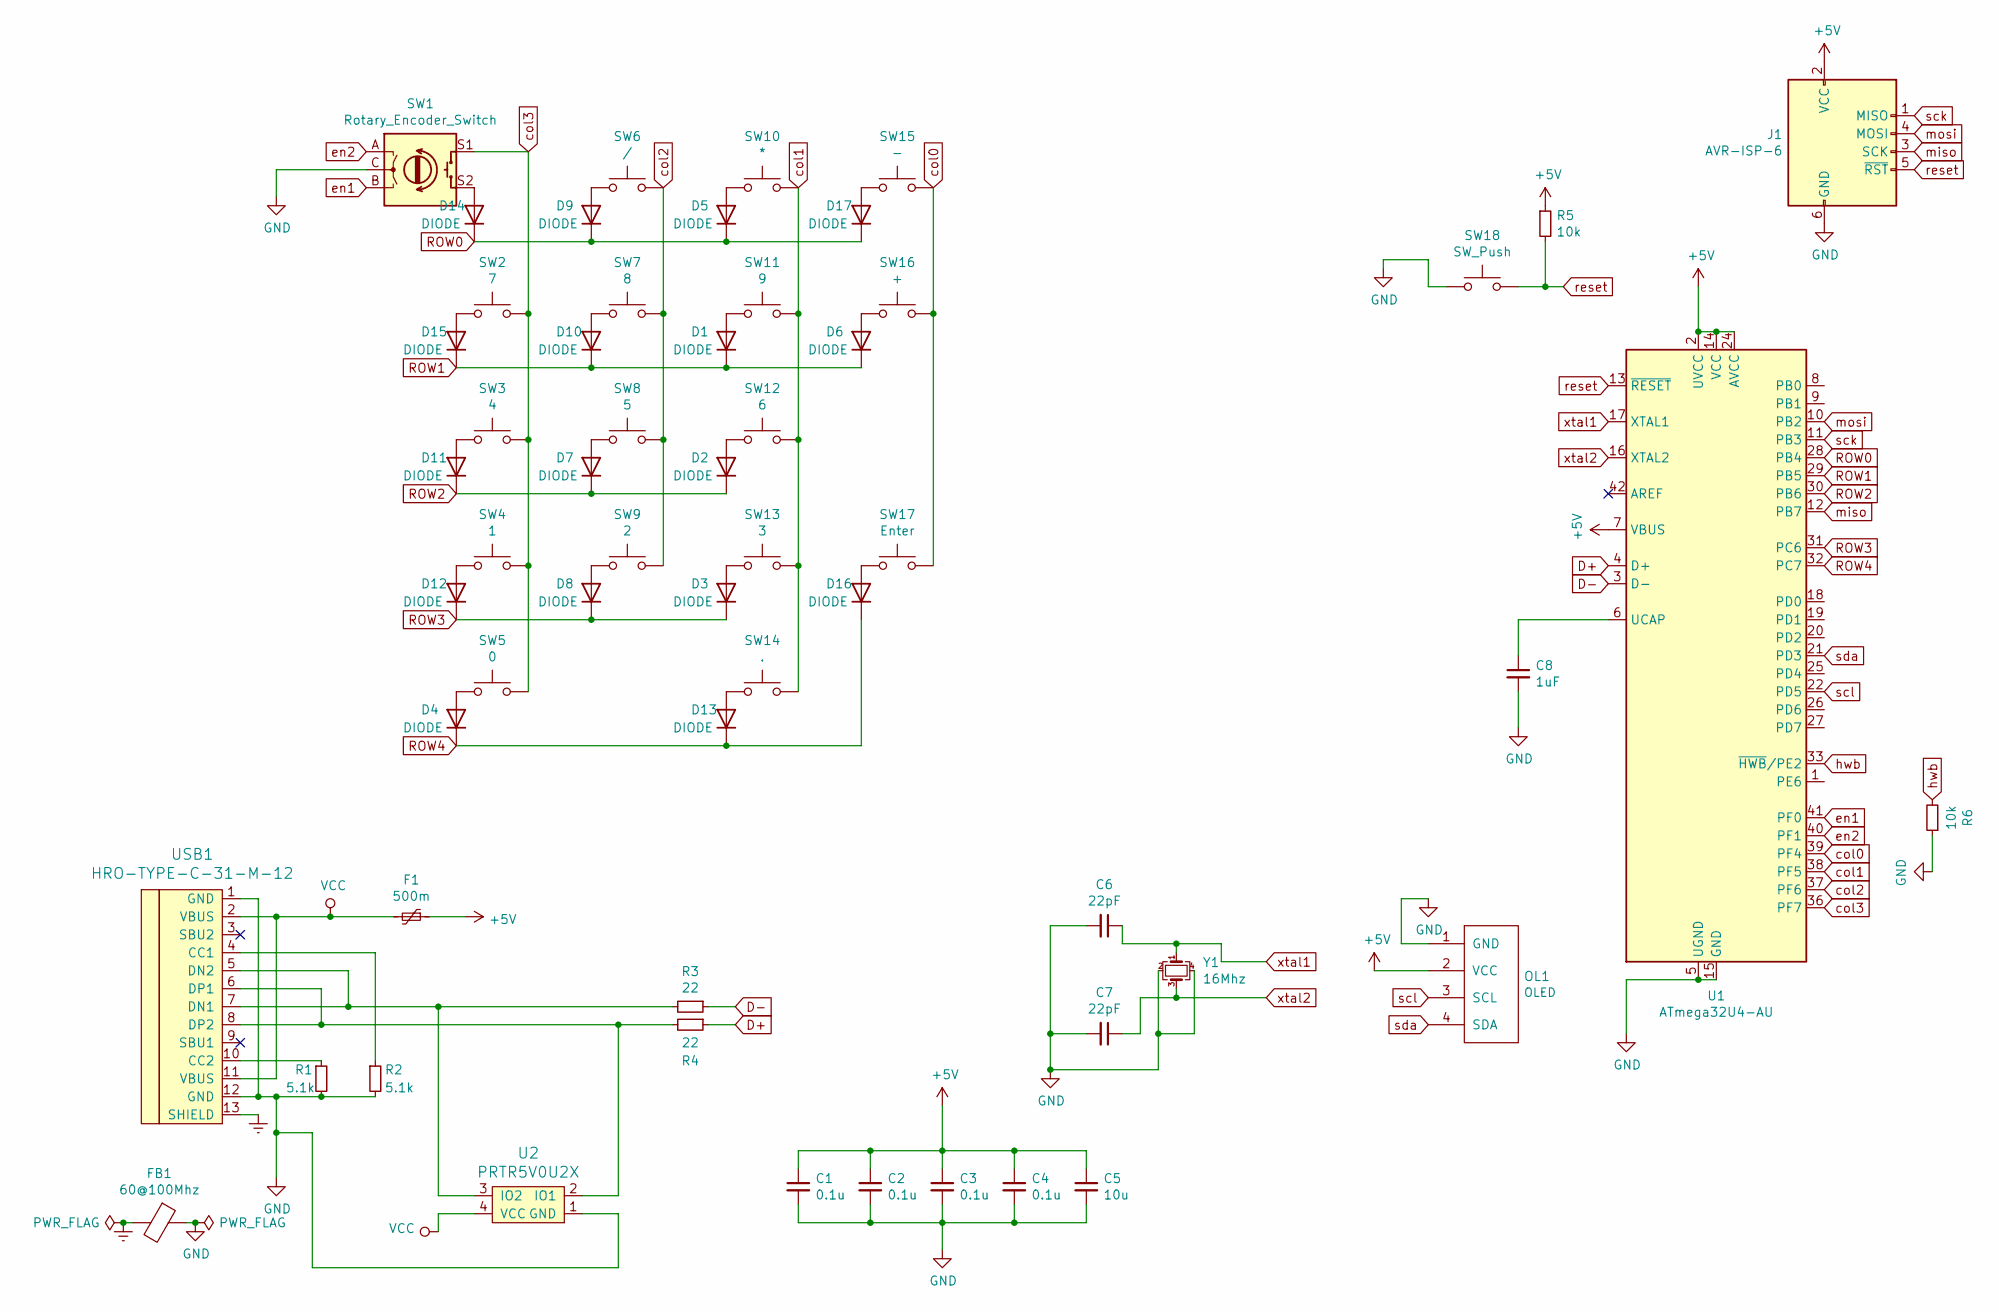
[picture p70: schematic MacroPad.sch]

Parts:
C1, C2, C3, C4: 0.1u; C_0805_2012Metric_Pad1.15x1.40mm_HandSolder
C5: 10u; C_0805_2012Metric_Pad1.15x1.40mm_HandSolder
C6, C7: 22pF; C_0805_2012Metric_Pad1.15x1.40mm_HandSolder
C8: 1uF; C_0805_2012Metric_Pad1.15x1.40mm_HandSolder
D1, D2, D3, D4, D5, D6, D7, D8, D9, D10, D11, D12, D13, D14, D15, D16, D17: DIODE; D_SOD123_axial
F1: 500m; Fuse_1206_3216Metric_Pad1.42x1.75mm_HandSolder
FB1: 60@100Mhz; L_0805_2012Metric_Pad1.15x1.40mm_HandSolder
J1: AVR-ISP-6; AVR_ICSP_3x2
OL1: OLED; SSD1306-0.91-OLED-4pin-128x32
R1, R2: 5.1k; R_0805_2012Metric_Pad1.15x1.40mm_HandSolder
R3, R4: 22; R_0805_2012Metric_Pad1.15x1.40mm_HandSolder
R5, R6: 10k; R_0805_2012Metric_Pad1.15x1.40mm_HandSolder
SW1: Rotary_Encoder_Switch; RotaryEncoder_Alps_EC11E-Switch_Vertical_H20mm
SW2: 7; Kailh_socket_MX
SW3: 4; Kailh_socket_MX
SW4: 1; Kailh_socket_MX
SW5: 0; Kailh_socket_MX
SW6: /; Kailh_socket_MX
SW7: 8; Kailh_socket_MX
SW8: 5; Kailh_socket_MX
SW9: 2; Kailh_socket_MX
SW10: *; Kailh_socket_MX
SW11: 9; Kailh_socket_MX
SW12: 6; Kailh_socket_MX
SW13: 3; Kailh_socket_MX
SW14: .; Kailh_socket_MX
SW15: -; Kailh_socket_MX
SW16: +; Kailh_socket_MX
SW17: Enter; Kailh_socket_MX
SW18: SW_Push; SW_SPST_SKQG_WithStem
U1: ATmega32U4-AU; TQFP-44_10x10mm_P0.8mm
U2: PRTR5V0U2X; tm-kicad-library-master_tm-kicad-lib.pretty_PRTR5V0U2X,215
USB1: HRO-TYPE-C-31-M-12; HRO-TYPE-C-31-M-12-HandSoldering
Y1: 16Mhz; Crystal_SMD_3225-4Pin_3.2x2.5mm_HandSoldering

Connections:
+5V: C1.1, C2.1, C3.1, C4.1, C5.1, F1.1, J1.2 (VCC), OL1.2 (VCC), R5.1, U1.2 (UVCC), U1.7 (VBUS), U1.14 (VCC), U1.24 (AVCC), U1.34 (VCC), U1.44 (AVCC)
D+: R4.1, U1.4 (D+)
D-: R3.1, U1.3 (D-)
Earth: FB1.2, USB1.13 (SHIELD)
GND: C1.2, C2.2, C3.2, C4.2, C5.2, C6.2, C7.2, C8.2, FB1.1, J1.6 (GND), OL1.1 (GND), R1.2, R2.2, R6.1, SW1.C, SW18.1, U1.5 (UGND), U1.15 (GND), U1.23 (GND), U1.35 (GND), U1.43 (GND), U2.1 (GND), USB1.1 (GND), USB1.12 (GND), Y1.2, Y1.4
unnamed: C8.1, U1.6 (UCAP)
unnamed: D1.1 (A), SW11.1
unnamed: D2.1 (A), SW12.1
unnamed: D3.1 (A), SW13.1
unnamed: D4.1 (A), SW5.1
unnamed: D5.1 (A), SW10.1
unnamed: D6.1 (A), SW16.1
unnamed: D7.1 (A), SW8.1
unnamed: D8.1 (A), SW9.1
unnamed: D9.1 (A), SW6.1
unnamed: D10.1 (A), SW7.1
unnamed: D11.1 (A), SW3.1
unnamed: D12.1 (A), SW4.1
unnamed: D13.1 (A), SW14.1
unnamed: D14.1 (A), SW1.S2
unnamed: D15.1 (A), SW2.1
unnamed: D16.1 (A), SW17.1
unnamed: D17.1 (A), SW15.1
unnamed: R1.1, USB1.10 (CC2)
unnamed: R2.1, USB1.4 (CC1)
unnamed: R3.2, U2.3 (IO2), USB1.5 (DN2), USB1.7 (DN1)
unnamed: R4.2, U2.2 (IO1), USB1.6 (DP1), USB1.8 (DP2)
ROW0: D5.2 (K), D9.2 (K), D14.2 (K), D17.2 (K), U1.28 (PB4)
ROW1: D1.2 (K), D6.2 (K), D10.2 (K), D15.2 (K), U1.29 (PB5)
ROW2: D2.2 (K), D7.2 (K), D11.2 (K), U1.30 (PB6)
ROW3: D3.2 (K), D8.2 (K), D12.2 (K), U1.31 (PC6)
ROW4: D4.2 (K), D13.2 (K), D16.2 (K), U1.32 (PC7)
VCC: F1.2, U2.4 (VCC), USB1.2 (VBUS), USB1.11 (VBUS)
col0: SW15.2, SW16.2, SW17.2, U1.39 (PF4)
col1: SW10.2, SW11.2, SW12.2, SW13.2, SW14.2, U1.38 (PF5)
col2: SW6.2, SW7.2, SW8.2, SW9.2, U1.37 (PF6)
col3: SW1.S1, SW2.2, SW3.2, SW4.2, SW5.2, U1.36 (PF7)
en1: SW1.B, U1.41 (PF0)
en2: SW1.A, U1.40 (PF1)
hwb: R6.2, U1.33 (~HWB~/PE2)
miso: J1.3 (SCK), U1.12 (PB7)
mosi: J1.4 (MOSI), U1.10 (PB2)
reset: J1.5 (~RST), R5.2, SW18.2, U1.13 (~RESET)
sck: J1.1 (MISO), U1.11 (PB3)
scl: OL1.3 (SCL), U1.22 (PD5)
sda: OL1.4 (SDA), U1.21 (PD3)
xtal1: C6.1, U1.17 (XTAL1), Y1.1
xtal2: C7.1, U1.16 (XTAL2), Y1.3

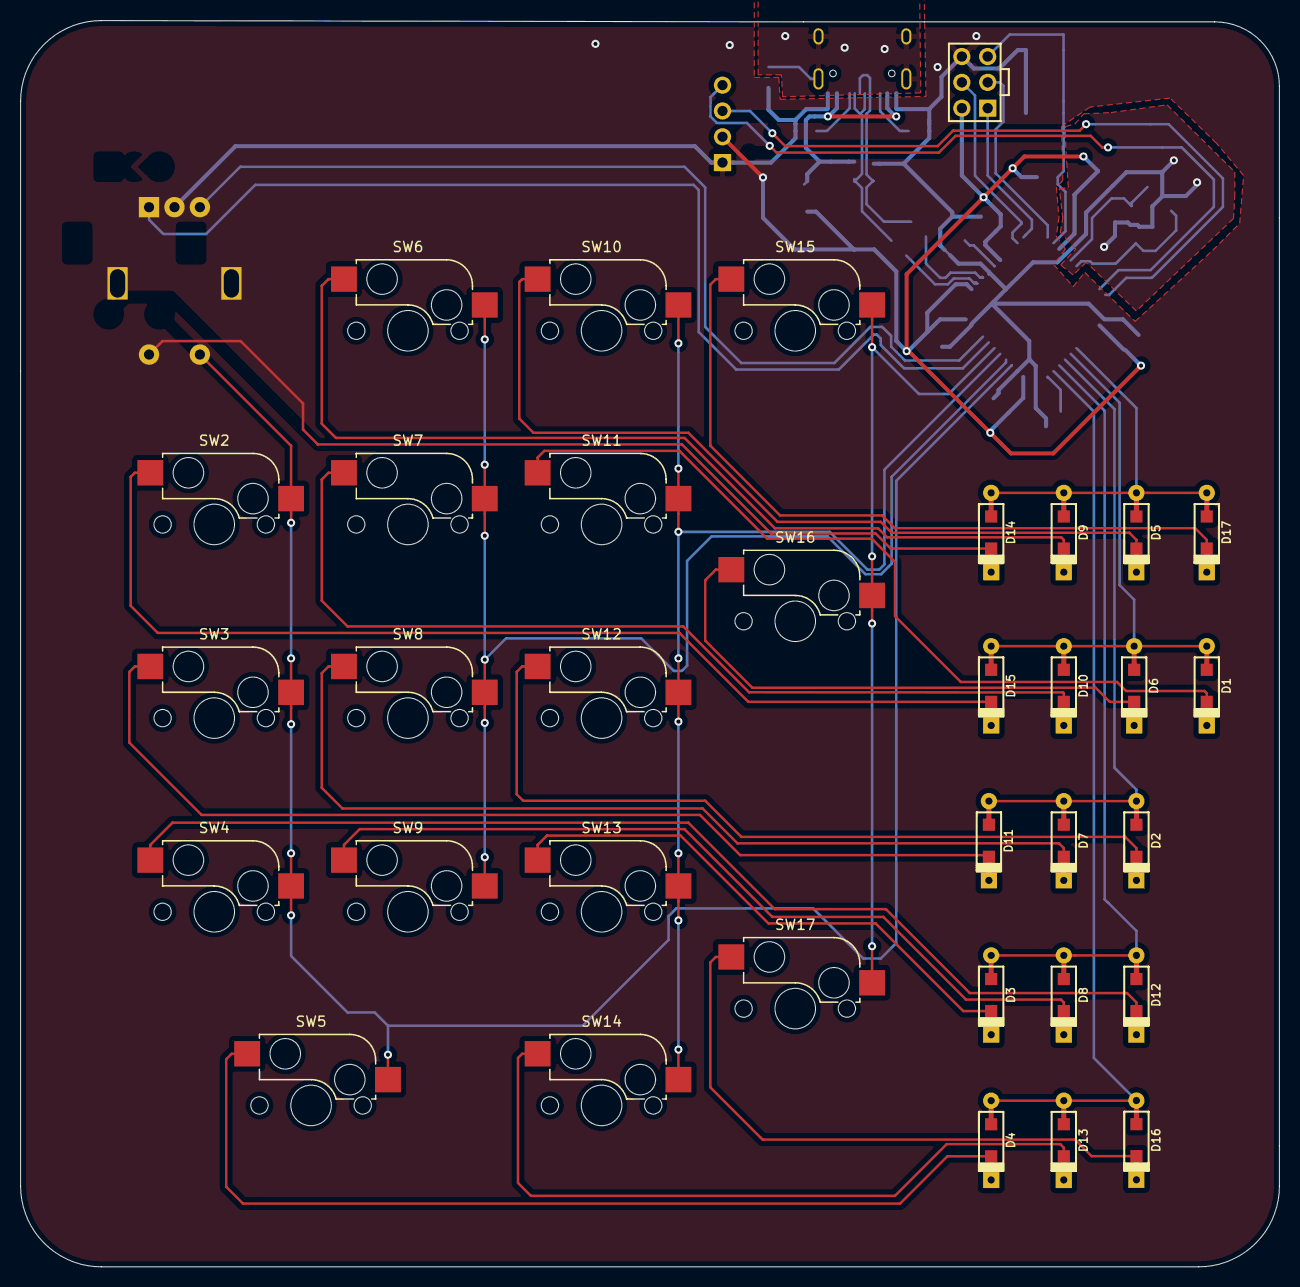
[picture p71: board MacroPad.kicad_pcb from above]

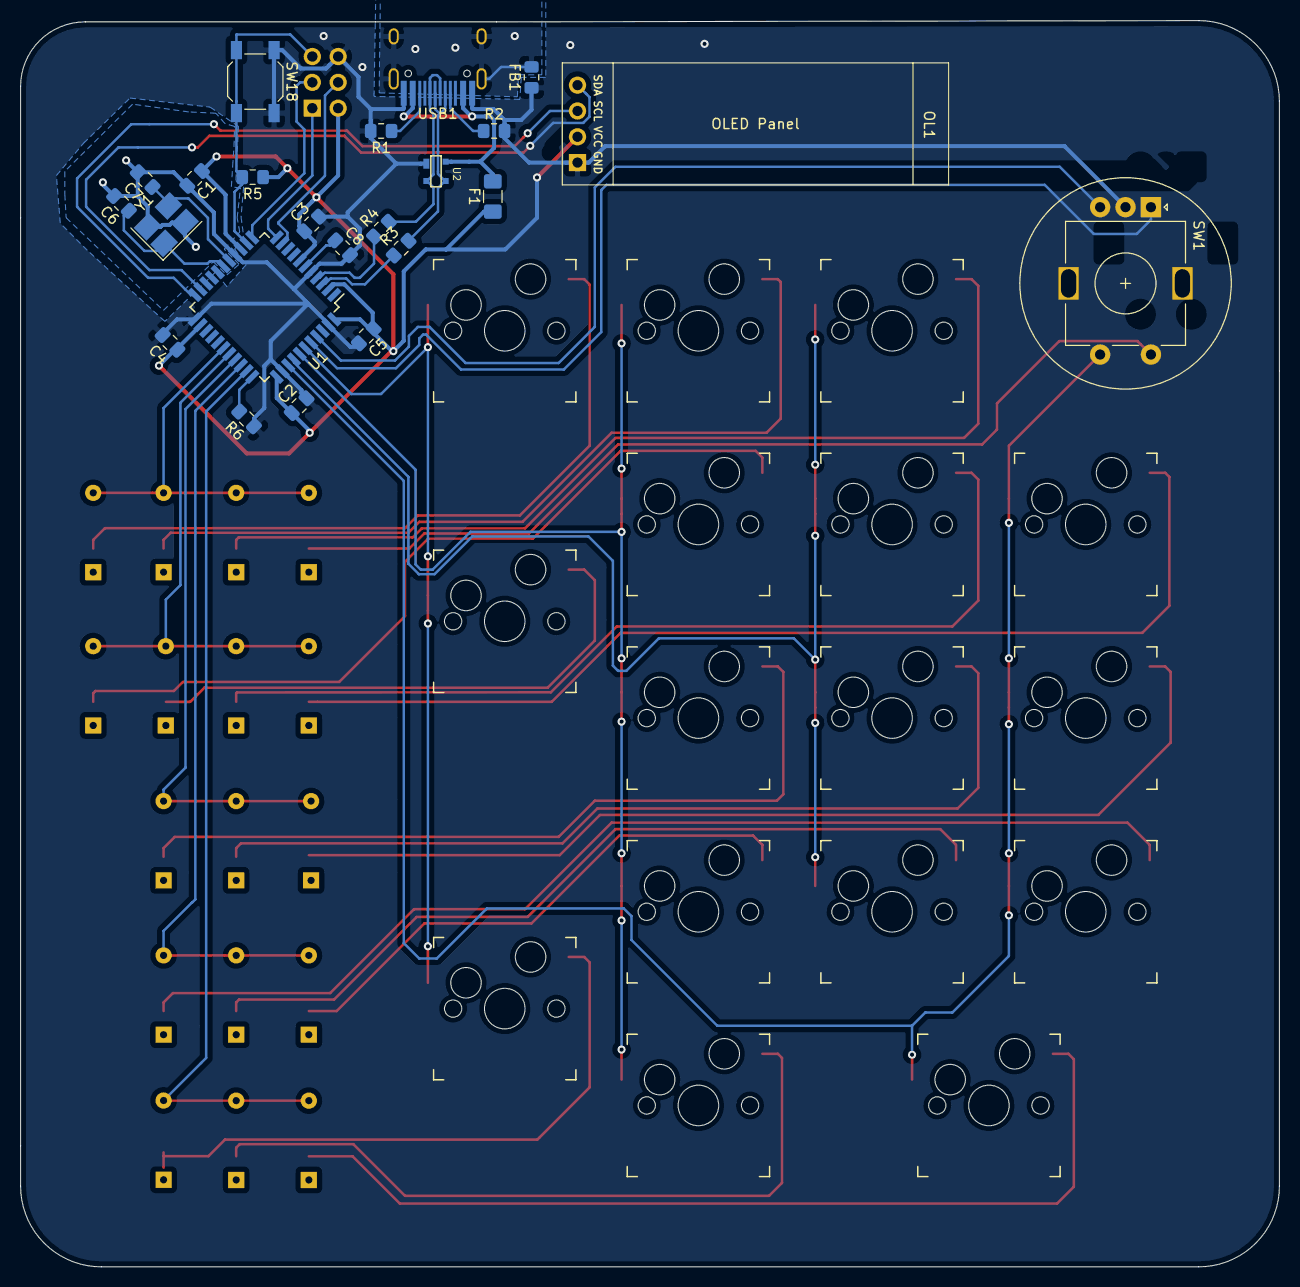
[picture p72: board MacroPad.kicad_pcb from below]

Board: 2 copper layers, 123.8 x 122.6 mm, 57 parts (39 on the bottom side), 48 nets.
